jnthas/pixie/project/sprites/happy.gif

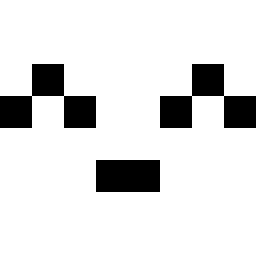
project/sprites/happy.gif
