jnthas/pixie/project/sprites/sun.gif

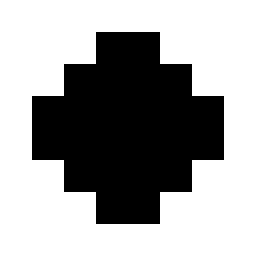
project/sprites/sun.gif
