jnthas/pixie/src/IdleExpression.h

#ifndef IdleExpression_h
#define IdleExpression_h

#include <Arduino.h>
#include "Expression.h"
#include "State.h"


class IdleExpression: public Expression {
  private:
    const unsigned int SLEEPING_TIME_TO_SLEEP = DecisionMaker::waitSomeTime(SLEEPING_MAX_TIMEOUT);
    unsigned long timeout = 0;
    
  public:
    bool evaluate(Sensors& sensors, State& state) override;
};

#endif
