jnthas/pixie/src/SleepingExpression.h

#ifndef SleepingExpression_h
#define SleepingExpression_h

#include <Arduino.h>
#include "Expression.h"
#include "State.h"

class SleepingExpression: public Expression {
  private:
    const unsigned int SLEEPING_TIME_TO_WAKEUP = DecisionMaker::waitSomeTime(SLEEPING_MAX_TIMEOUT);
    unsigned long timeout = 0;
    
  public:
    bool evaluate(Sensors& sensors, State& state) override;
};

#endif
