jnthas/pixie/src/GlobalDefinition.h

#include <Arduino.h>

/* Uncomment to enable printing out nice debug messages. */
//#define PIXIE_DEBUG

#define DEBUG_PRINTER                                                           \
  Serial 

/* Setup debug printing macros. */
#ifdef PIXIE_DEBUG
  #define DEBUG_PRINT(...)                                                       \
    { DEBUG_PRINTER.print(__VA_ARGS__); }
  #define DEBUG_PRINTLN(...)                                                     \
    { DEBUG_PRINTER.println(__VA_ARGS__); }
#else
  #define DEBUG_PRINT(...)                                                       \
    {} /**< Debug Print Placeholder if Debug is disabled */
  #define DEBUG_PRINTLN(...)                                                     \
    {} /**< Debug Print Line Placeholder if Debug is disabled */
#endif
